rage-ace/kidz/software/coral/snaps/img0000.jpg

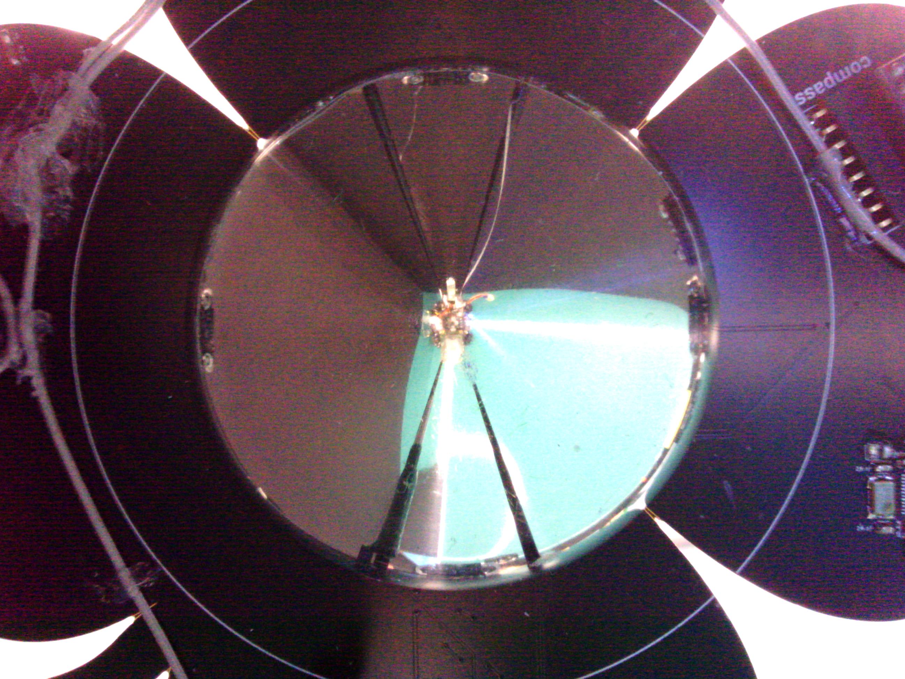
software/coral/snaps/img0000.jpg
