rage-ace/kidz/software/coral/snaps/img0003.jpg

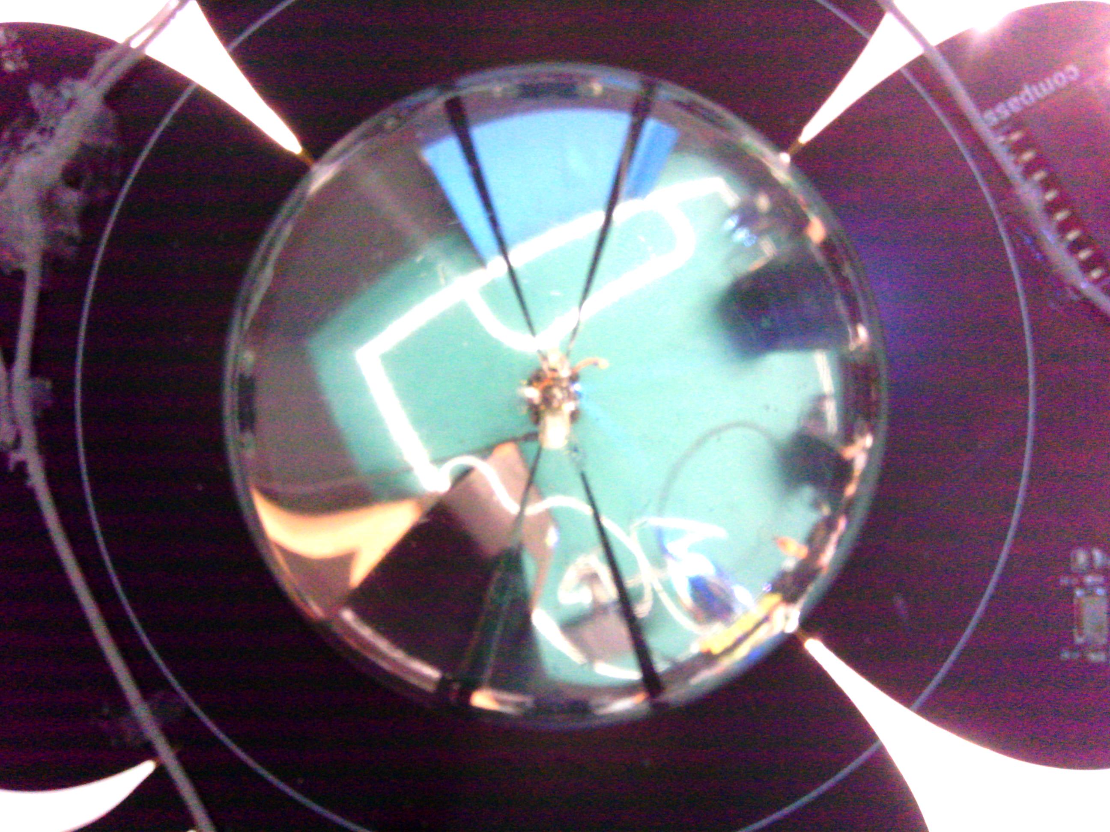
software/coral/snaps/img0003.jpg
