rage-ace/kidz/software/coral/snaps/img0004.jpg

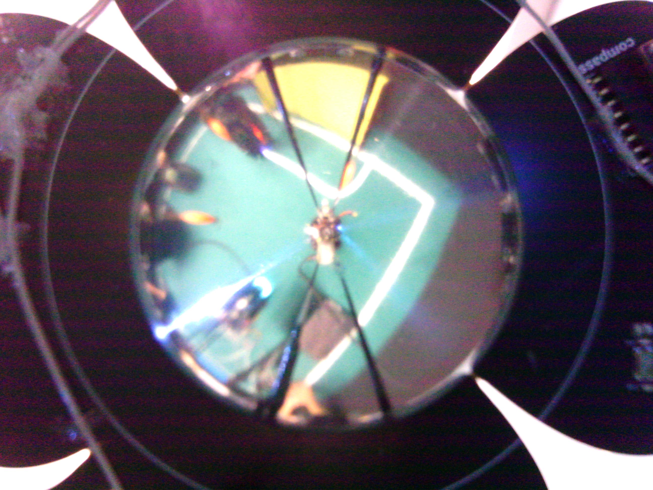
software/coral/snaps/img0004.jpg
