rage-ace/kidz/software/coral/snaps/img0005.jpg

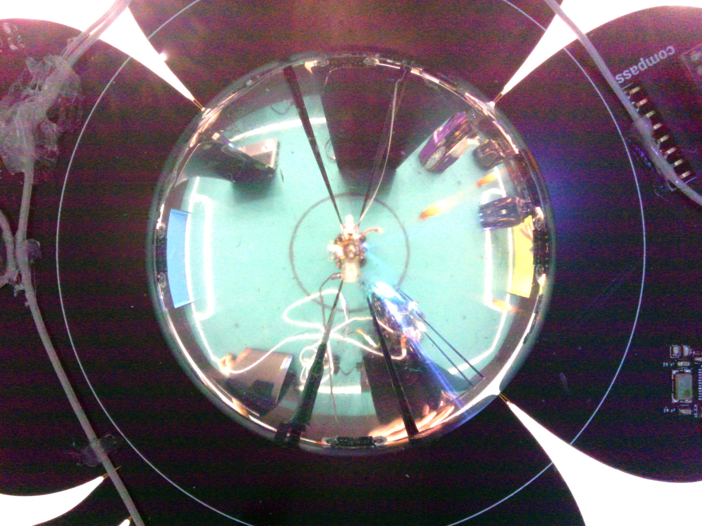
software/coral/snaps/img0005.jpg
