rage-ace/kidz/software/microcontrollers/include/vector.h

#ifndef VECTOR_H
#define VECTOR_H

#include <cmath>

struct Point {
    float x;
    float y;

    bool operator==(const Point &other) const {
        return x == other.x && y == other.y;
    }

    bool operator!=(const Point &other) const { return !(*this == other); }
};

class Vector {
  public:
    Vector(float angle = NAN, float distance = NAN);
    static Vector fromPoint(Point point);

    float angle;
    float distance;

    Vector &operator=(const Vector &other);
    Vector operator+(const Vector &other) const;
    Vector operator-() const;
    Vector operator-(const Vector &other) const;
    Vector operator*(const float other) const;
    Vector operator/(const float other) const;

    bool exists() const { return !std::isnan(angle) && !std::isnan(distance); }
};

#endif
